azerimaker/ButaBoard/ButaBoard-Software/ButaBoard-v1-Arduino/Buta-Button-Read/Buta-Button-Read.ino

int pushButton = 4;

// the setup routine runs once when you press reset:
void setup() {
  // initialize serial communication at 9600 bits per second:
  Serial.begin(9600);
  // make the pushbutton's pin an input:
  pinMode(pushButton, INPUT);
}

// the loop routine runs over and over again forever:
void loop() {
  // read the input pin:
  int buttonState = digitalRead(pushButton);
  // print out the state of the button:
  Serial.println(buttonState);
  delay(10);        // delay in between reads for stability
}
