azerimaker/ButaBoard/ButaBoard-Software/ButaBoard-v1-Arduino/Buta-LED-Test1/Buta-LED-Test1.ino

#include <Adafruit_NeoPixel.h>
#ifdef __AVR__
  #include <avr/power.h>
#endif

#define LED_PIN 17
#define LED_NUMBER 12
Adafruit_NeoPixel buta = Adafruit_NeoPixel(LED_NUMBER, LED_PIN, NEO_GRB + NEO_KHZ800);

void setup() {
  buta.begin();
  buta.show(); // Initialize all pixels to 'off'
}

void loop() {
  // Some example procedures showing how to display to the pixels:
  colorWipe(buta.Color(255, 0, 0), 100); // Red
  colorWipe(buta.Color(0, 255, 0), 100); // Green
  colorWipe(buta.Color(0, 0, 255), 100); // Blue
//colorWipe(buta.Color(0, 0, 0, 255), 50); // White RGBW

  // Send a theater pixel chase in...
  theaterChase(buta.Color(127, 127, 127), 50); // White
  theaterChase(buta.Color(127, 0, 0), 50); // Red
  theaterChase(buta.Color(0, 0, 127), 50); // Blue

  rainbow(20);
  rainbowCycle(20);
  theaterChaseRainbow(50);
}

// Fill the dots one after the other with a color
void colorWipe(uint32_t c, uint8_t wait) {
  for(uint16_t i=0; i<buta.numPixels(); i++) {
    buta.setPixelColor(i, c);
    buta.show();
    delay(wait);
  }
}

void rainbow(uint8_t wait) {
  uint16_t i, j;

  for(j=0; j<256; j++) {
    for(i=0; i<buta.numPixels(); i++) {
      buta.setPixelColor(i, Wheel((i+j) & 255));
    }
    buta.show();
    delay(wait);
  }
}

// Slightly different, this makes the rainbow equally distributed throughout
void rainbowCycle(uint8_t wait) {
  uint16_t i, j;

  for(j=0; j<256*5; j++) { // 5 cycles of all colors on wheel
    for(i=0; i< buta.numPixels(); i++) {
      buta.setPixelColor(i, Wheel(((i * 256 / buta.numPixels()) + j) & 255));
    }
    buta.show();
    delay(wait);
  }
}

//Theatre-style crawling lights.
void theaterChase(uint32_t c, uint8_t wait) {
  for (int j=0; j<10; j++) {  //do 10 cycles of chasing
    for (int q=0; q < 3; q++) {
      for (uint16_t i=0; i < buta.numPixels(); i=i+3) {
        buta.setPixelColor(i+q, c);    //turn every third pixel on
      }
      buta.show();

      delay(wait);

      for (uint16_t i=0; i < buta.numPixels(); i=i+3) {
        buta.setPixelColor(i+q, 0);        //turn every third pixel off
      }
    }
  }
}

//Theatre-style crawling lights with rainbow effect
void theaterChaseRainbow(uint8_t wait) {
  for (int j=0; j < 256; j++) {     // cycle all 256 colors in the wheel
    for (int q=0; q < 3; q++) {
      for (uint16_t i=0; i < buta.numPixels(); i=i+3) {
        buta.setPixelColor(i+q, Wheel( (i+j) % 255));    //turn every third pixel on
      }
      buta.show();

      delay(wait);

      for (uint16_t i=0; i < buta.numPixels(); i=i+3) {
        buta.setPixelColor(i+q, 0);        //turn every third pixel off
      }
    }
  }
}

// Input a value 0 to 255 to get a color value.
// The colours are a transition r - g - b - back to r.
uint32_t Wheel(byte WheelPos) {
  WheelPos = 255 - WheelPos;
  if(WheelPos < 85) {
    return buta.Color(255 - WheelPos * 3, 0, WheelPos * 3);
  }
  if(WheelPos < 170) {
    WheelPos -= 85;
    return buta.Color(0, WheelPos * 3, 255 - WheelPos * 3);
  }
  WheelPos -= 170;
  return buta.Color(WheelPos * 3, 255 - WheelPos * 3, 0);
}
