azerimaker/ButaBoard/ButaBoard-Software/ButaBoard-v1-Arduino/Buta-Blink/Buta-Blink.ino

void setup() {
  pinMode(LED_BUILTIN, OUTPUT); // Pin D13
}

void loop() {
  digitalWrite(LED_BUILTIN, HIGH);   // turn the LED on (HIGH is the voltage level)
  delay(500);                       // wait for half a second
  digitalWrite(LED_BUILTIN, LOW);    // turn the LED off by making the voltage LOW
  delay(500);                       // wait for half a second
}
