azerimaker/ButaBoard/ButaBoard-Software/ButaBoard-v1-Arduino/Buta-Microphone-Test/Buta-Microphone-Test.ino

int soundPin = A4;
 
void setup()
{
  Serial.begin(9600);
}
 
void loop()
{

  /* 
     
    // with filtering
     
    long sum = 0;
    for(int i=0; i<100; i++)
    {
        sum += analogRead(soundPin);
    }
 
    sum = sum/100;
    Serial.println(sum);

    */

  
    Serial.println(analogRead(soundPin));
   // delay(1);
}
